Archive-663/olympusPENF/ASSETS/PHOTO/samplePOS_PENF (1).jpg

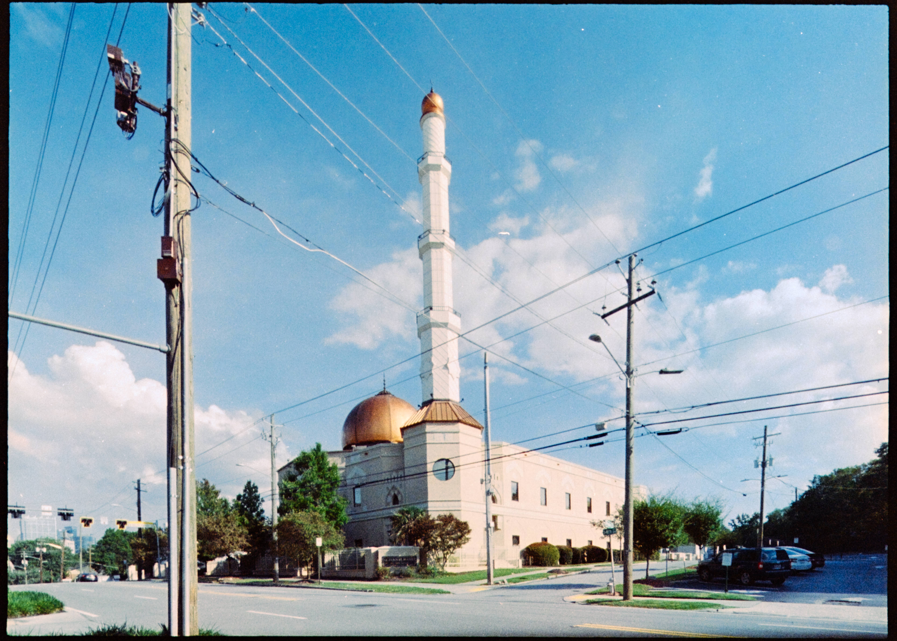
ASSETS/PHOTO/samplePOS_PENF (1).jpg
