Archive-663/olympusPENF/ASSETS/PHOTO/samplePOS_PENF (2).jpg

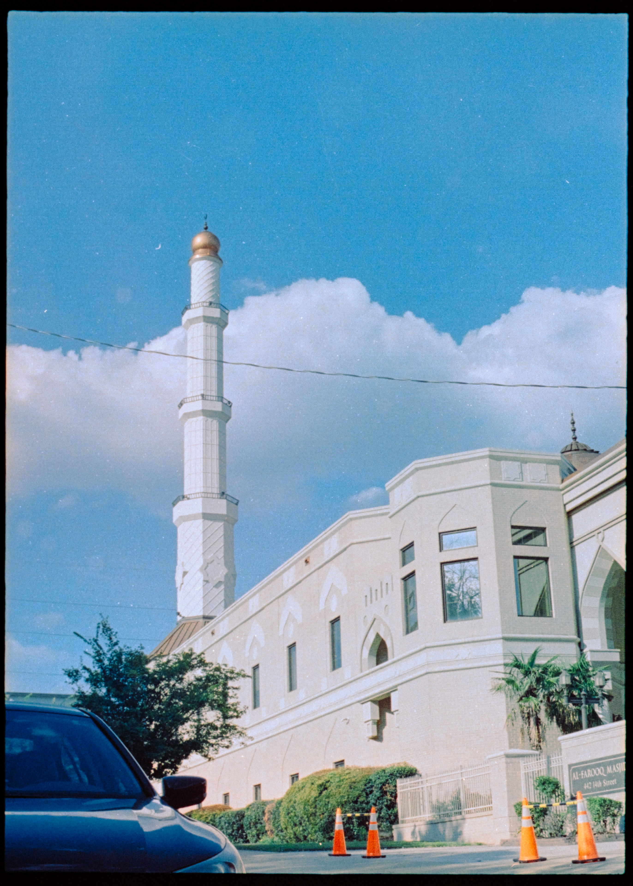
ASSETS/PHOTO/samplePOS_PENF (2).jpg
