Archive-663/olympusPENF/ASSETS/PHOTO/samplePOS_PENF (3).jpg

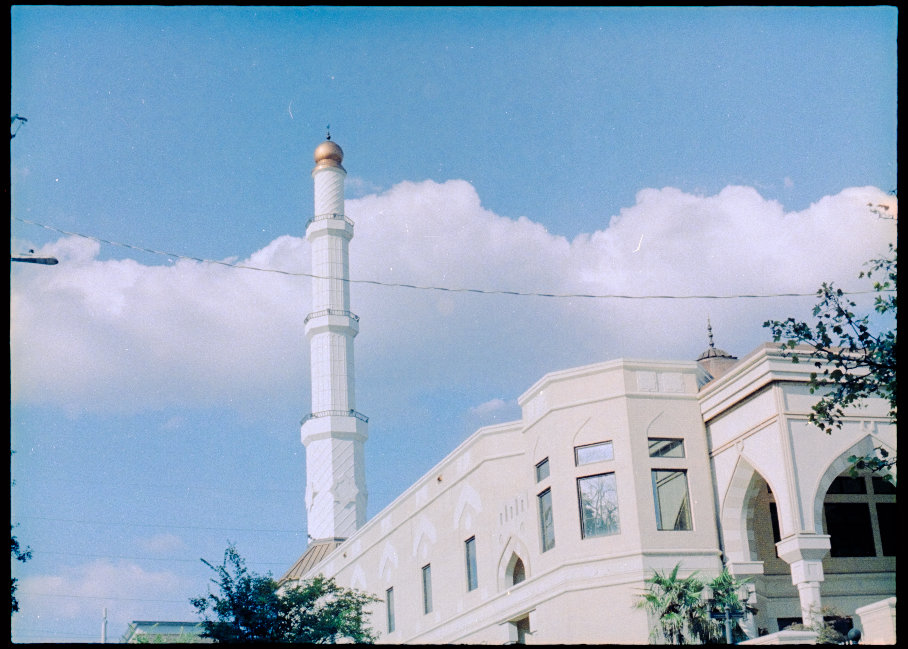
ASSETS/PHOTO/samplePOS_PENF (3).jpg
