Archive-663/olympusPENF/ASSETS/PHOTO/samplePOS_PENF (5).jpg

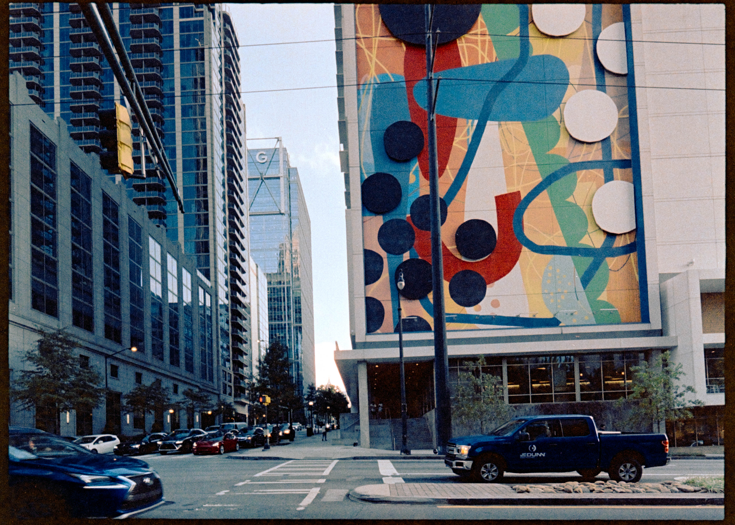
ASSETS/PHOTO/samplePOS_PENF (5).jpg
