Archive-663/olympusPENF/ASSETS/PHOTO/samplePOS_PENF (6).jpg

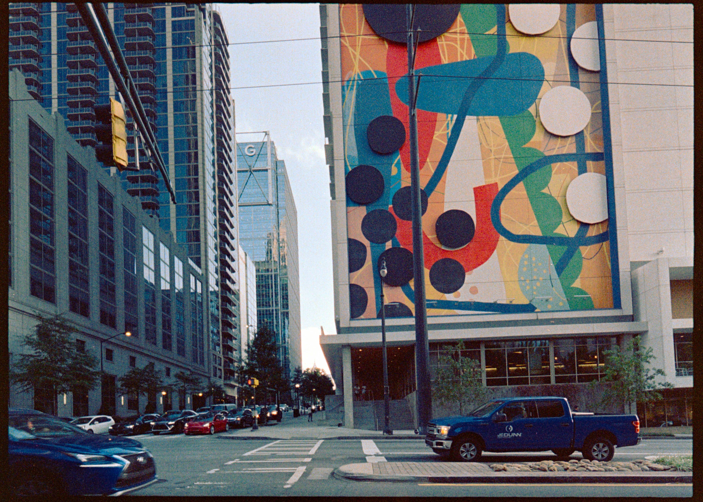
ASSETS/PHOTO/samplePOS_PENF (6).jpg
