Archive-663/olympusPENF/ASSETS/PHOTO/samplePOS_PENF (7).jpg

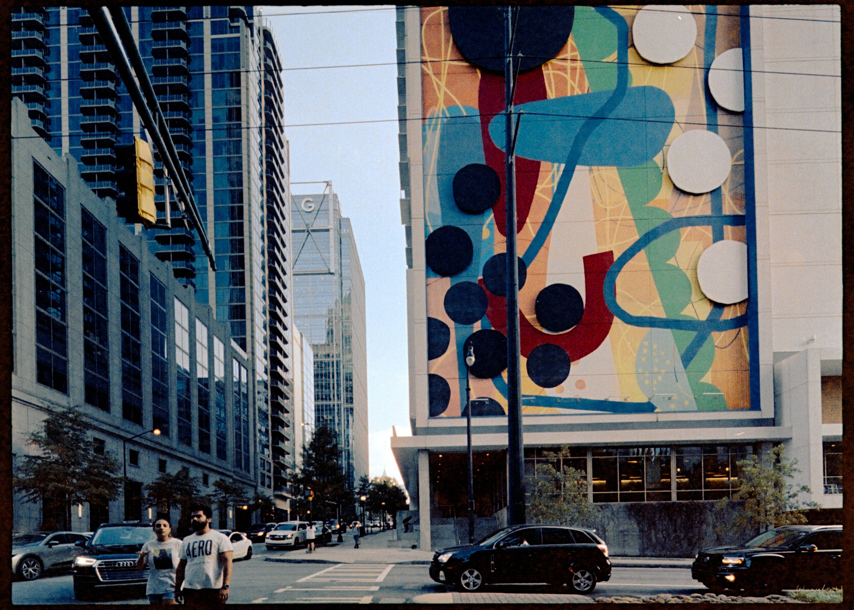
ASSETS/PHOTO/samplePOS_PENF (7).jpg
