Archive-663/olympusPENF/ASSETS/PHOTO/samplePOS_PENF (8).jpg

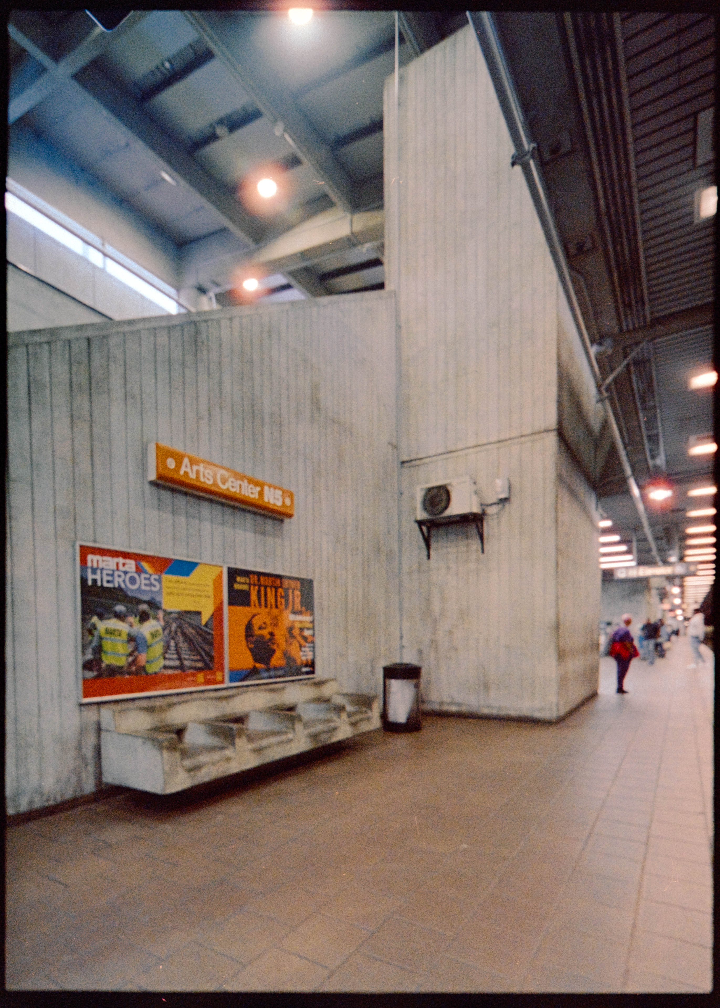
ASSETS/PHOTO/samplePOS_PENF (8).jpg
