Archive-663/olympusPENF/ASSETS/PHOTO/samplePOS_PENF (9).jpg

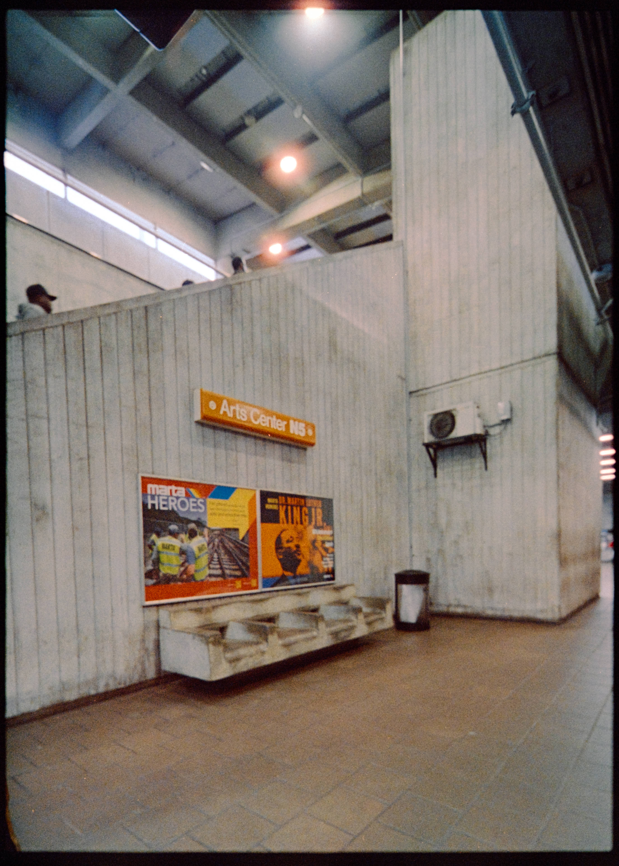
ASSETS/PHOTO/samplePOS_PENF (9).jpg
