Archive-663/olympusPENF/ASSETS/PHOTO/samplePOS_PENF (10).jpg

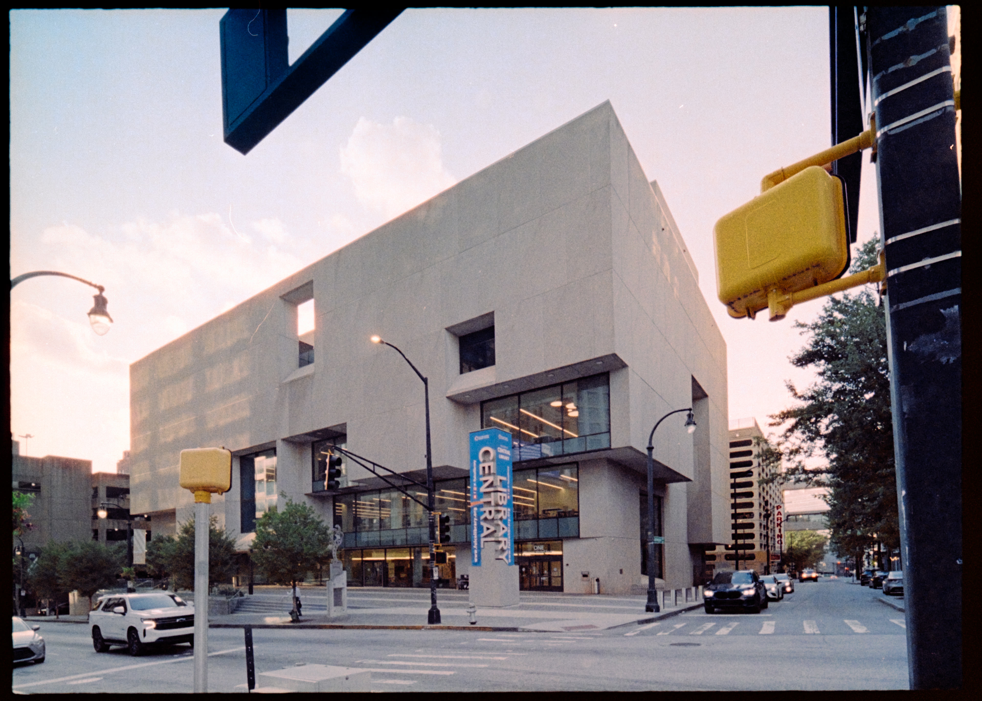
ASSETS/PHOTO/samplePOS_PENF (10).jpg
