Archive-663/olympusPENF/ASSETS/PHOTO/samplePOS_PENF (12).jpg

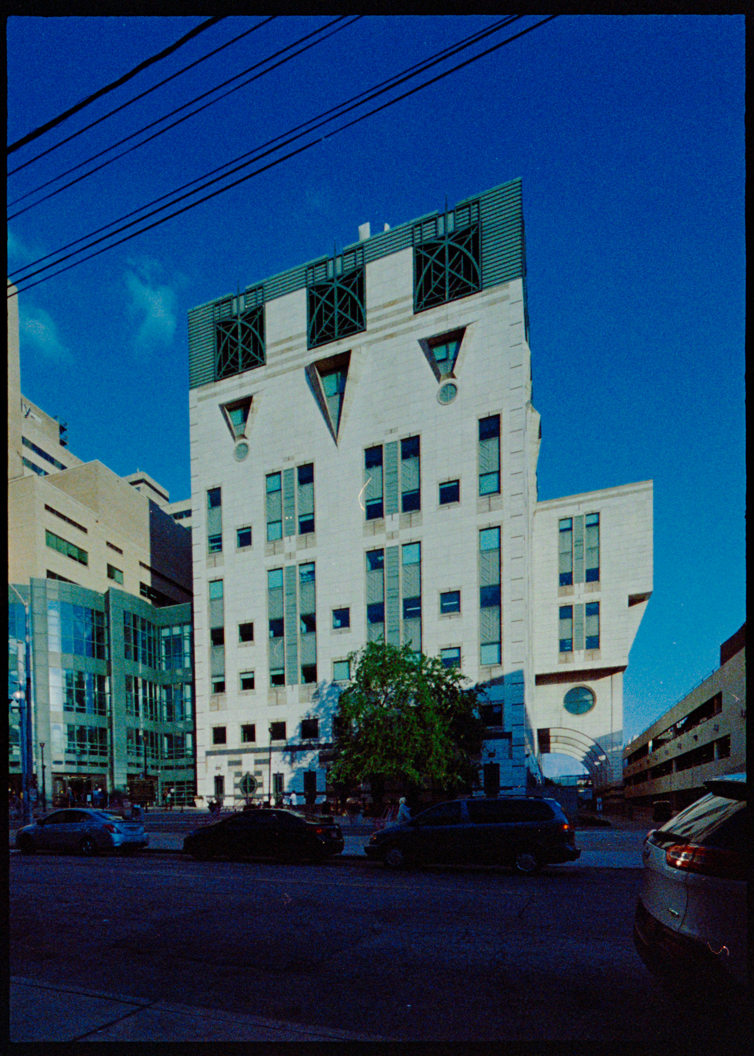
ASSETS/PHOTO/samplePOS_PENF (12).jpg
