Archive-663/olympusPENF/ASSETS/PHOTO/samplePOS_PENF (13).jpg

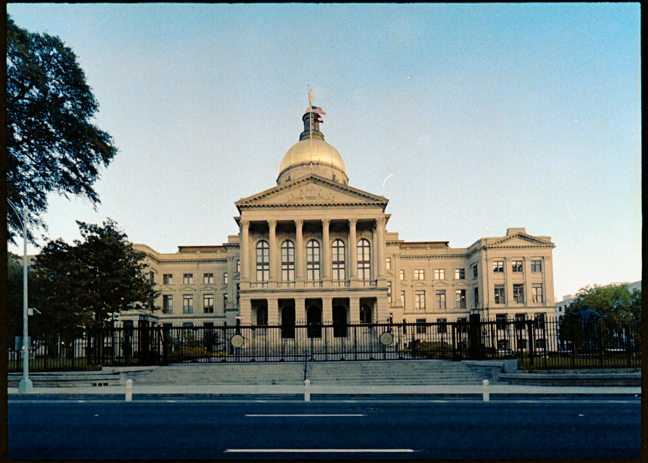
ASSETS/PHOTO/samplePOS_PENF (13).jpg
