Archive-663/olympusPENF/ASSETS/PHOTO/samplePOS_PENF (15).jpg

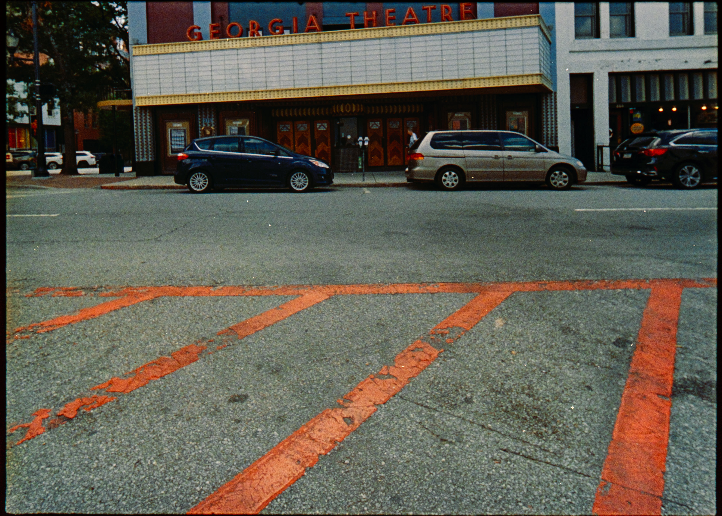
ASSETS/PHOTO/samplePOS_PENF (15).jpg
