Archive-663/olympusPENF/ASSETS/PHOTO/samplePOS_PENF (16).jpg

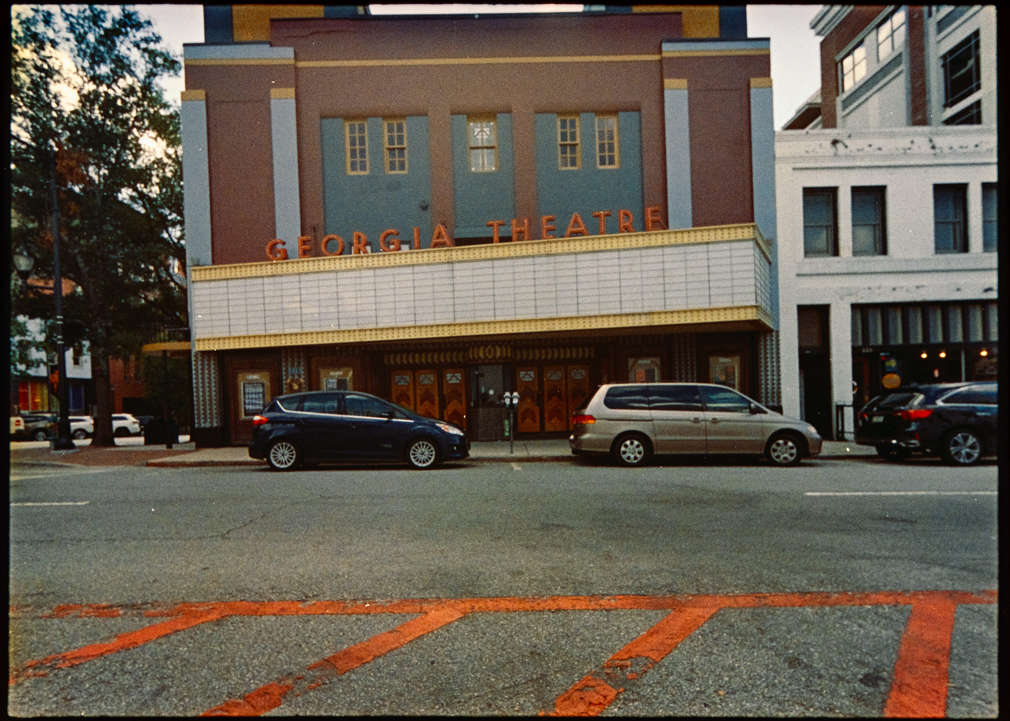
ASSETS/PHOTO/samplePOS_PENF (16).jpg
