Archive-663/olympusPENF/ASSETS/PHOTO/samplePOS_PENF (17).jpg

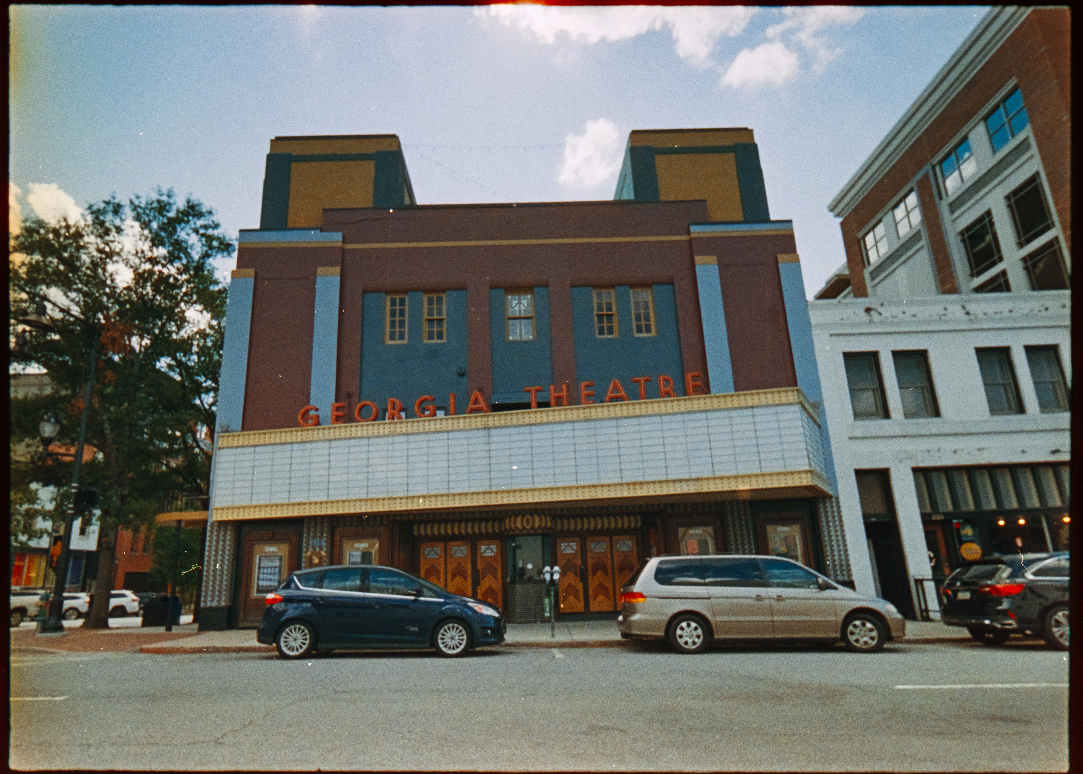
ASSETS/PHOTO/samplePOS_PENF (17).jpg
