Archive-663/olympusPENF/ASSETS/PHOTO/samplePOS_PENF (18).jpg

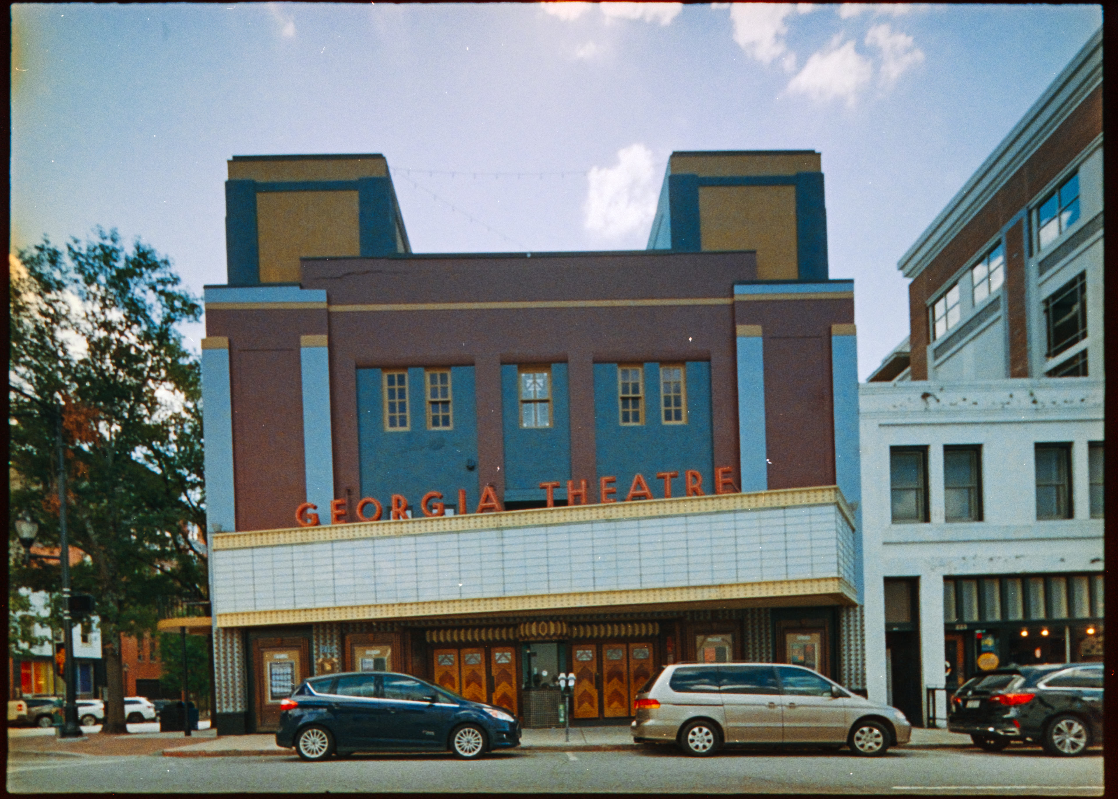
ASSETS/PHOTO/samplePOS_PENF (18).jpg
