Archive-663/olympusPENF/ASSETS/PHOTO/samplePOS_PENF (19).jpg

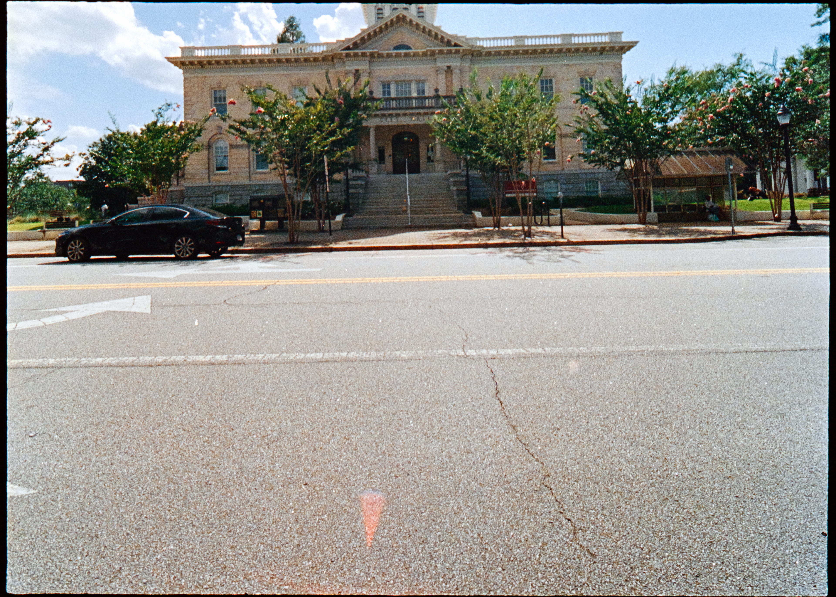
ASSETS/PHOTO/samplePOS_PENF (19).jpg
