Archive-663/olympusPENF/ASSETS/PHOTO/samplePOS_PENF (20).jpg

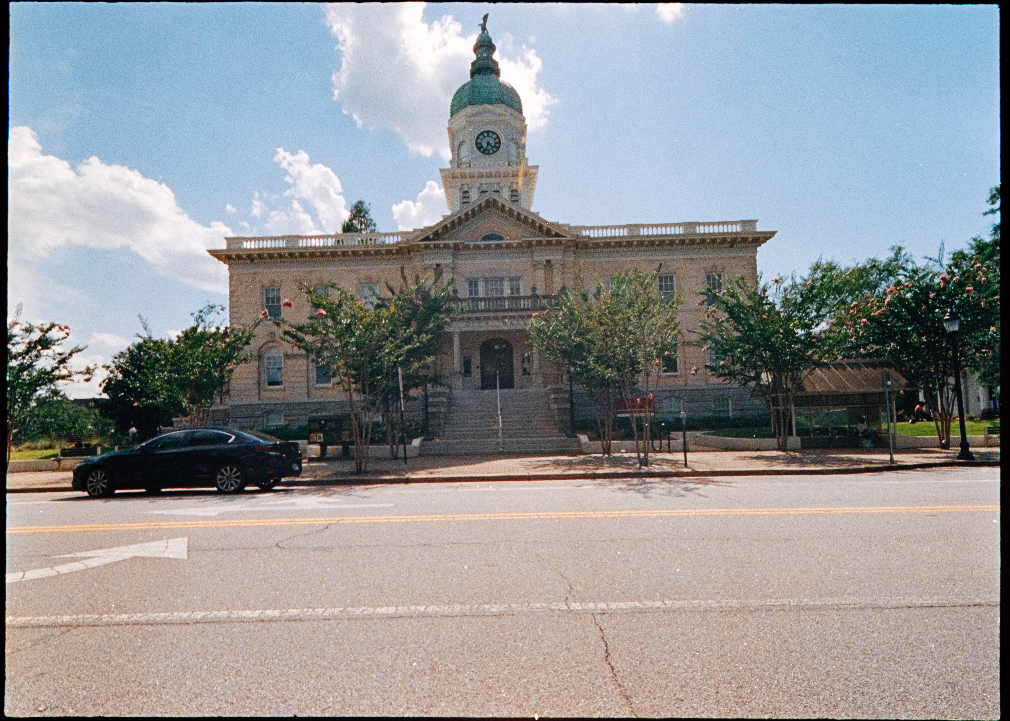
ASSETS/PHOTO/samplePOS_PENF (20).jpg
