Archive-663/olympusPENF/ASSETS/PHOTO/samplePOS_PENF (21).jpg

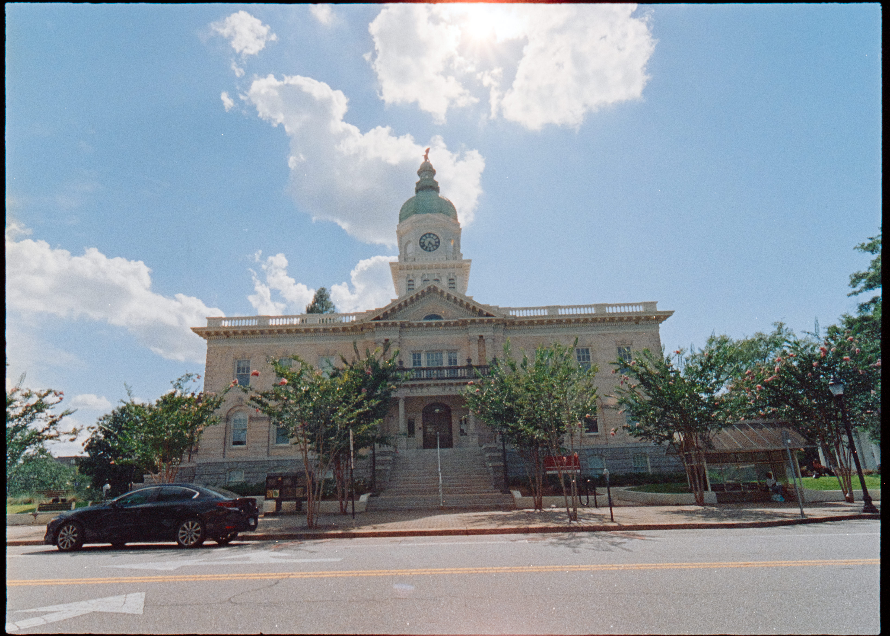
ASSETS/PHOTO/samplePOS_PENF (21).jpg
