Archive-663/olympusPENF/ASSETS/PHOTO/samplePOS_PENF (22).jpg

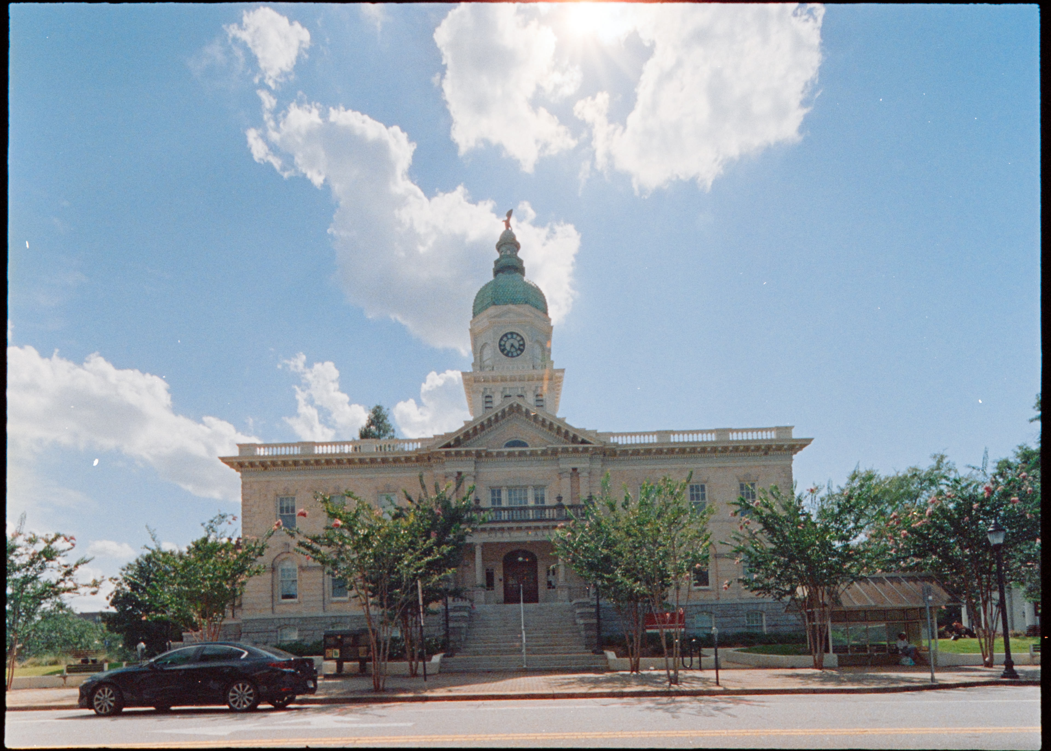
ASSETS/PHOTO/samplePOS_PENF (22).jpg
