Archive-663/olympusPENF/ASSETS/PHOTO/samplePOS_PENF (23).jpg

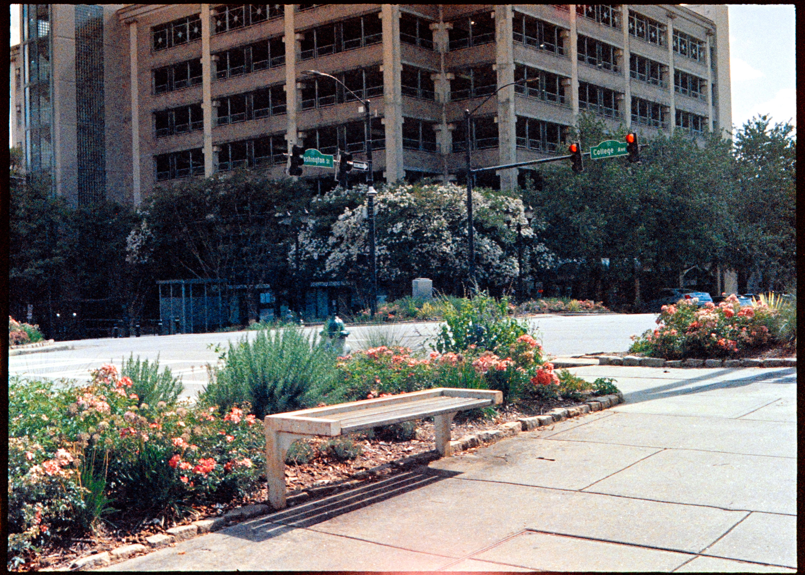
ASSETS/PHOTO/samplePOS_PENF (23).jpg
