Archive-663/olympusPENF/ASSETS/PHOTO/samplePOS_PENF (24).jpg

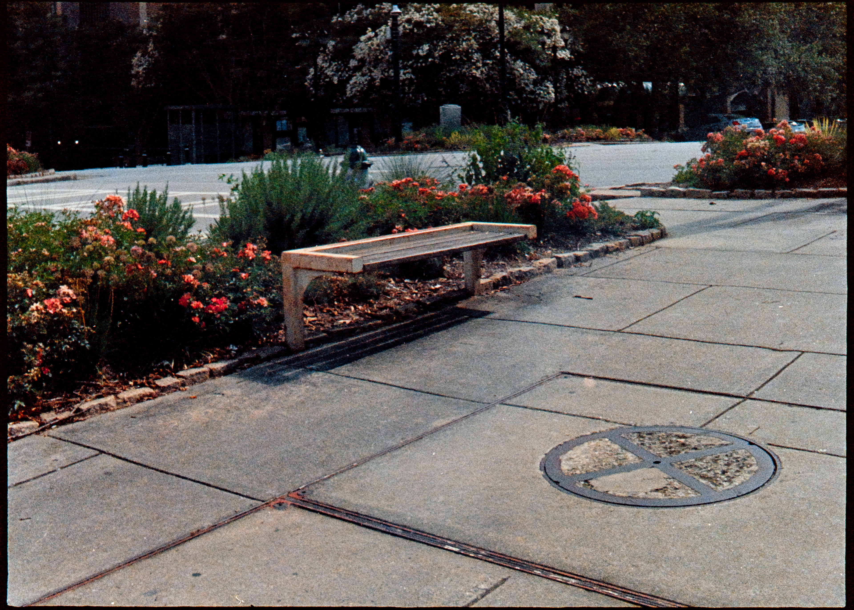
ASSETS/PHOTO/samplePOS_PENF (24).jpg
