Archive-663/olympusPENF/ASSETS/PHOTO/samplePOS_PENF (25).jpg

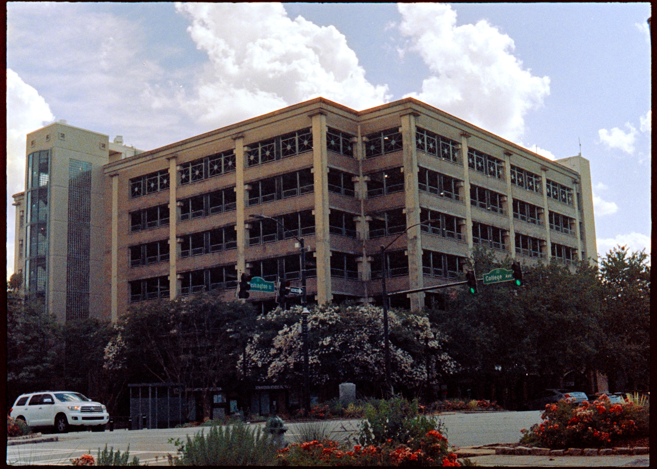
ASSETS/PHOTO/samplePOS_PENF (25).jpg
