Archive-663/olympusPENF/ASSETS/PHOTO/samplePOS_PENF (26).jpg

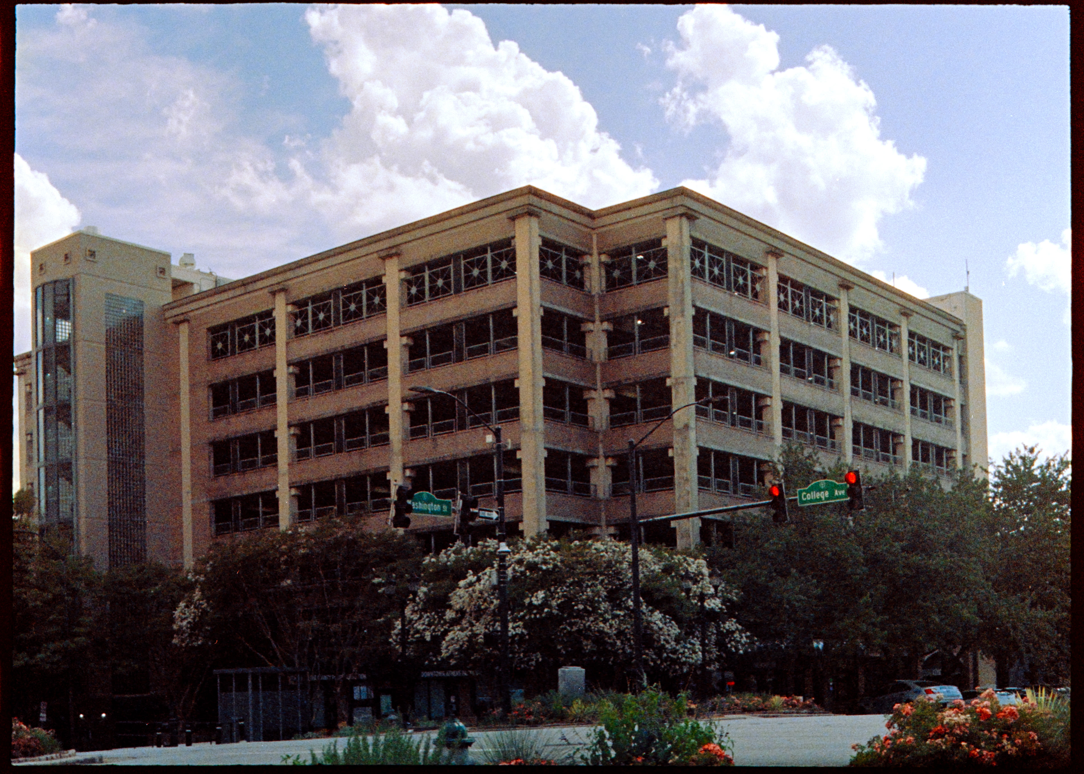
ASSETS/PHOTO/samplePOS_PENF (26).jpg
