Archive-663/olympusPENF/ASSETS/PHOTO/samplePOS_PENF (27).jpg

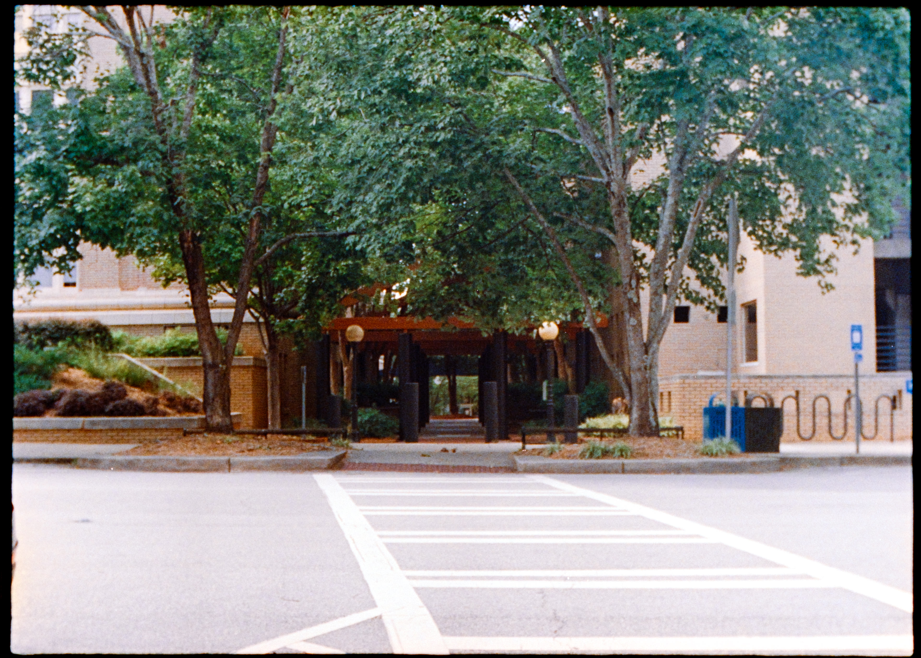
ASSETS/PHOTO/samplePOS_PENF (27).jpg
