Archive-663/olympusPENF/ASSETS/PHOTO/samplePOS_PENF (28).jpg

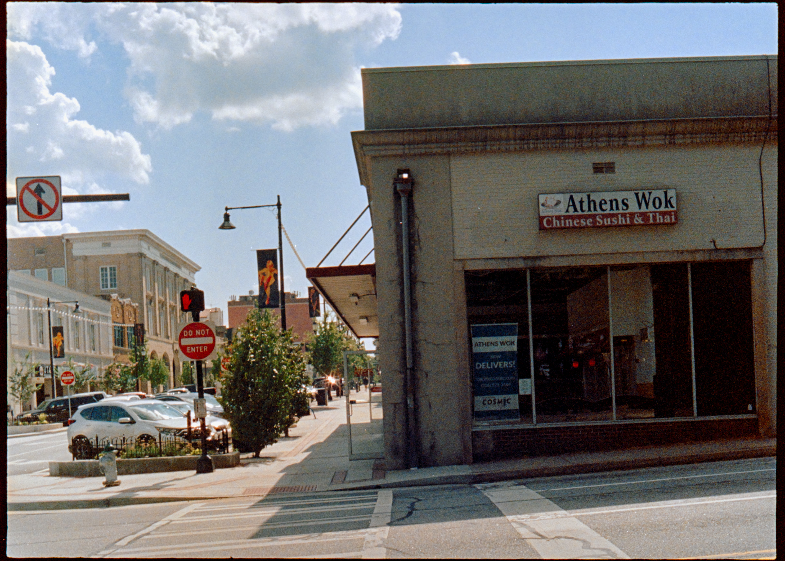
ASSETS/PHOTO/samplePOS_PENF (28).jpg
