Archive-663/olympusPENF/ASSETS/PHOTO/samplePOS_PENF (29).jpg

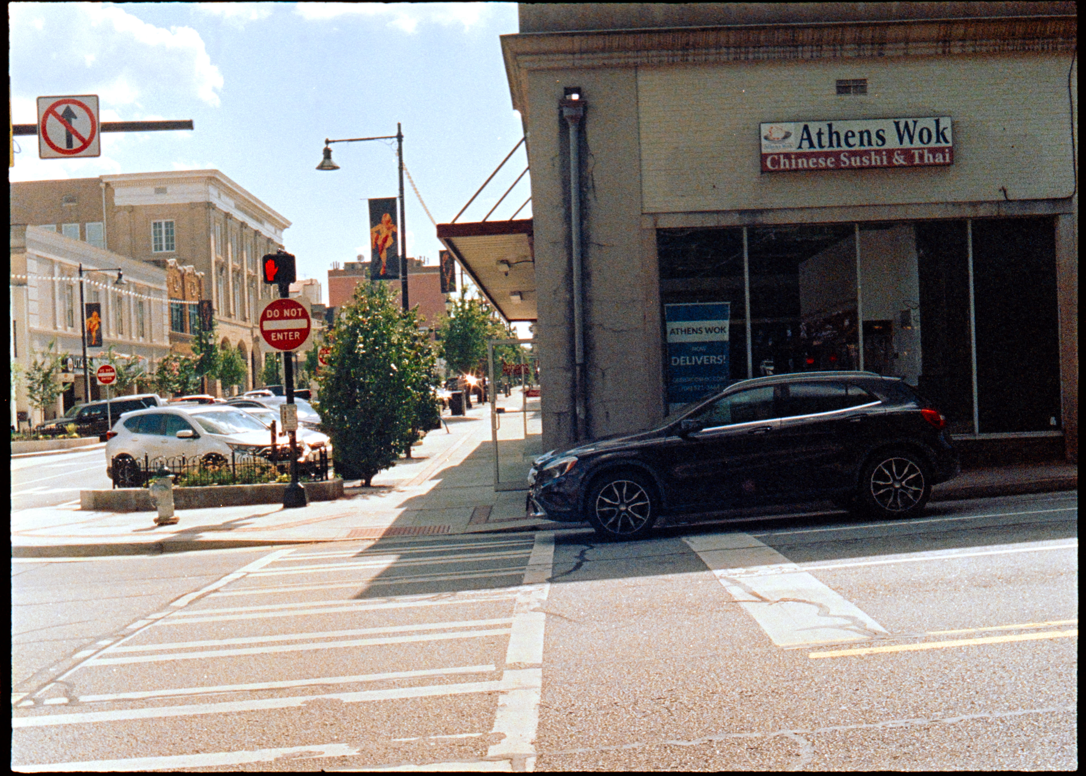
ASSETS/PHOTO/samplePOS_PENF (29).jpg
