Archive-663/olympusPENF/ASSETS/PHOTO/samplePOS_PENF (31).jpg

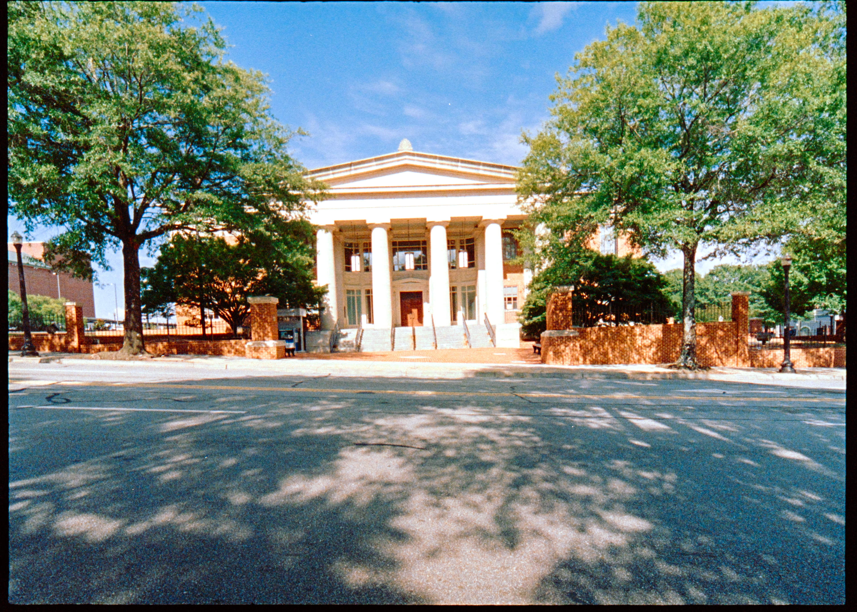
ASSETS/PHOTO/samplePOS_PENF (31).jpg
