Archive-663/olympusPENF/ASSETS/PHOTO/samplePOS_PENF (33).jpg

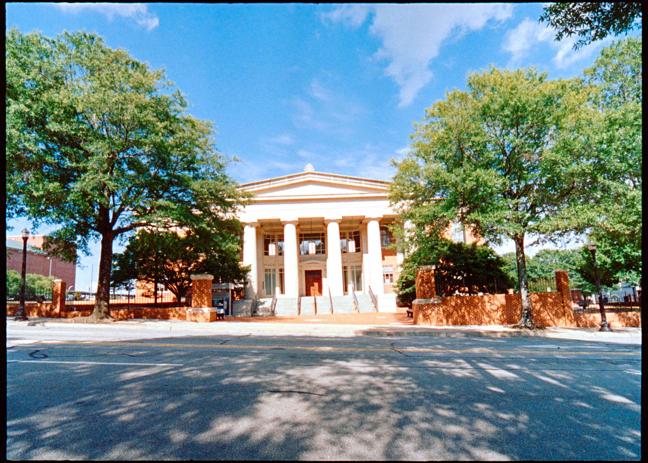
ASSETS/PHOTO/samplePOS_PENF (33).jpg
