Archive-663/olympusPENF/ASSETS/PHOTO/samplePOS_PENF (34).jpg

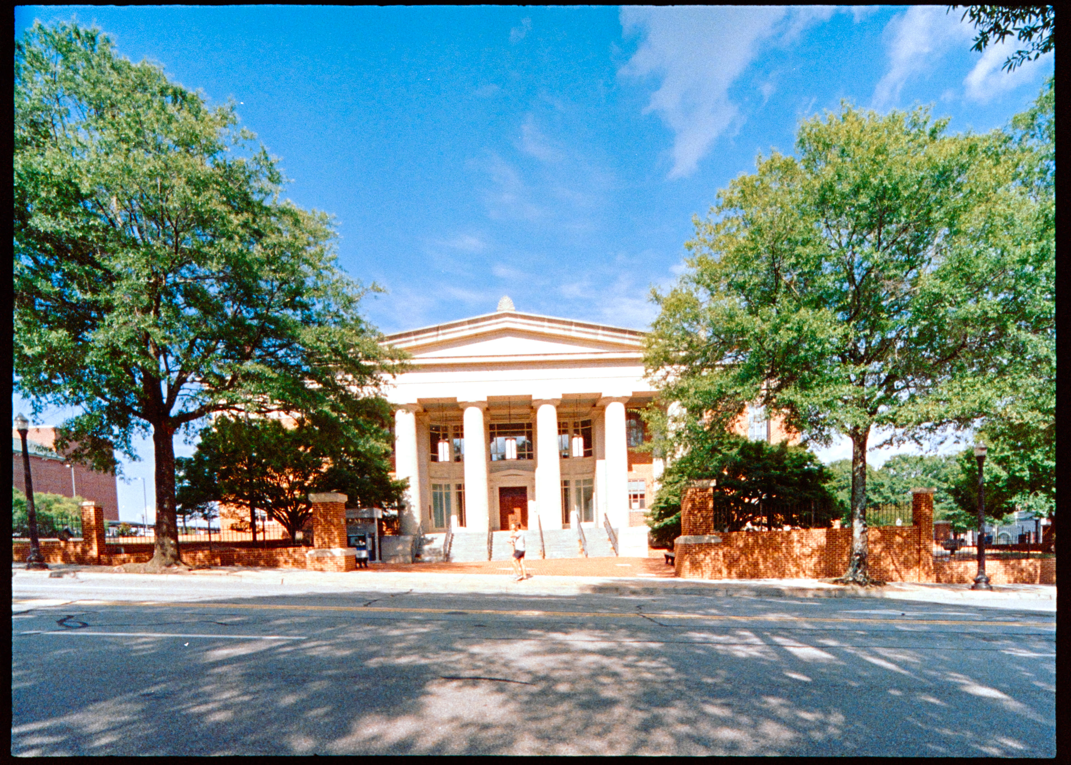
ASSETS/PHOTO/samplePOS_PENF (34).jpg
