Archive-663/olympusPENF/ASSETS/PHOTO/samplePOS_PENF (35).jpg

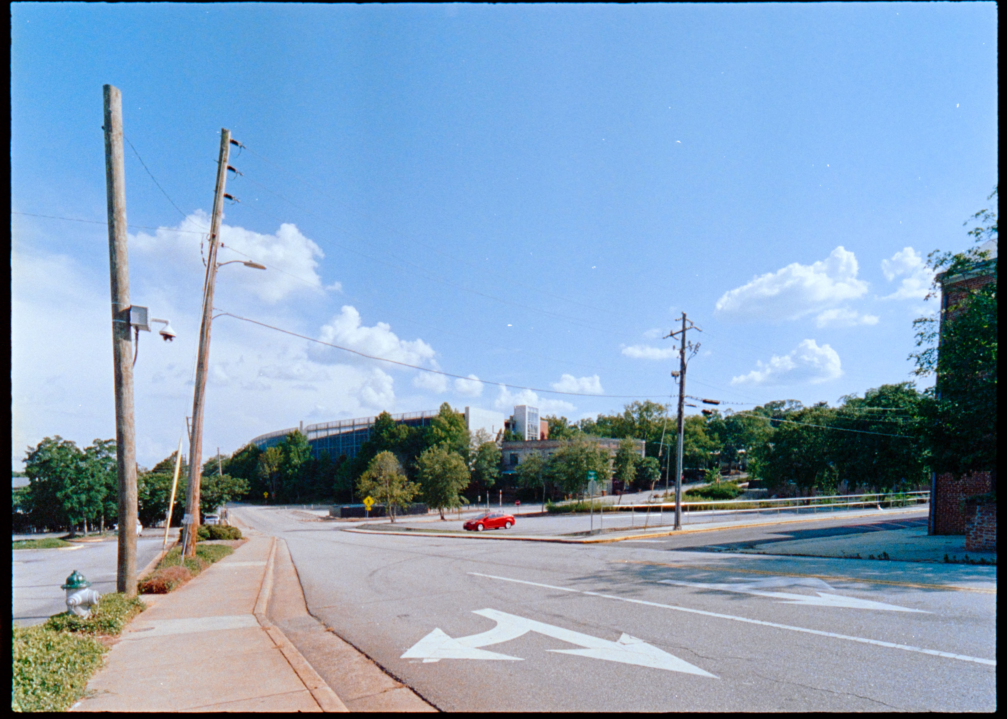
ASSETS/PHOTO/samplePOS_PENF (35).jpg
