Archive-663/olympusPENF/ASSETS/PHOTO/samplePOS_PENF (37).jpg

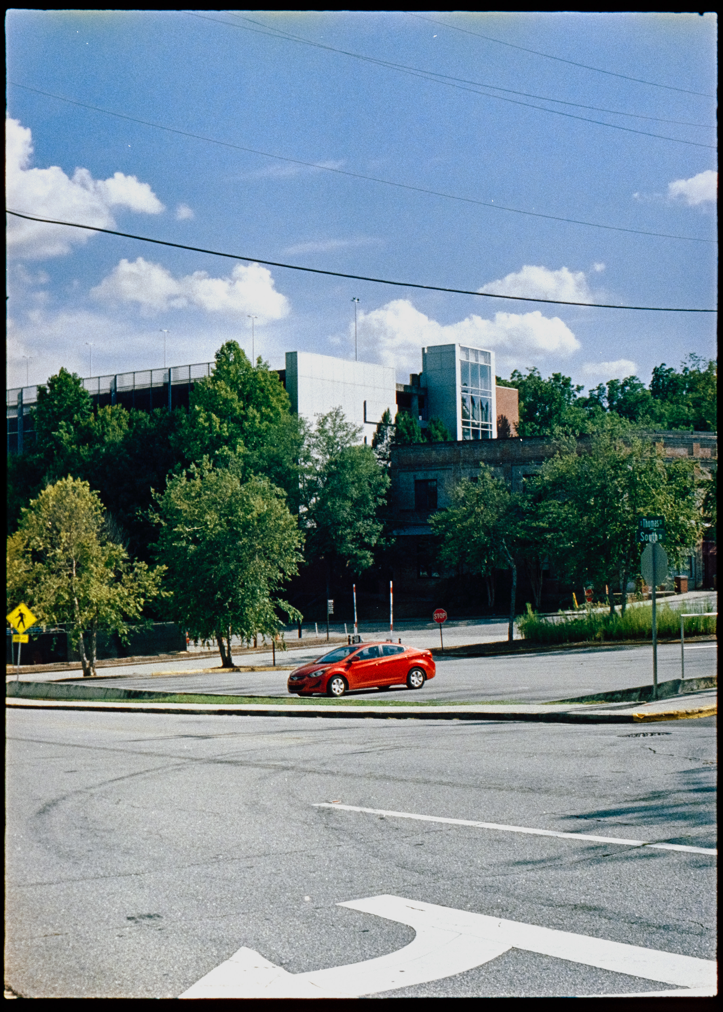
ASSETS/PHOTO/samplePOS_PENF (37).jpg
