Archive-663/olympusPENF/ASSETS/PHOTO/samplePOS_PENF (38).jpg

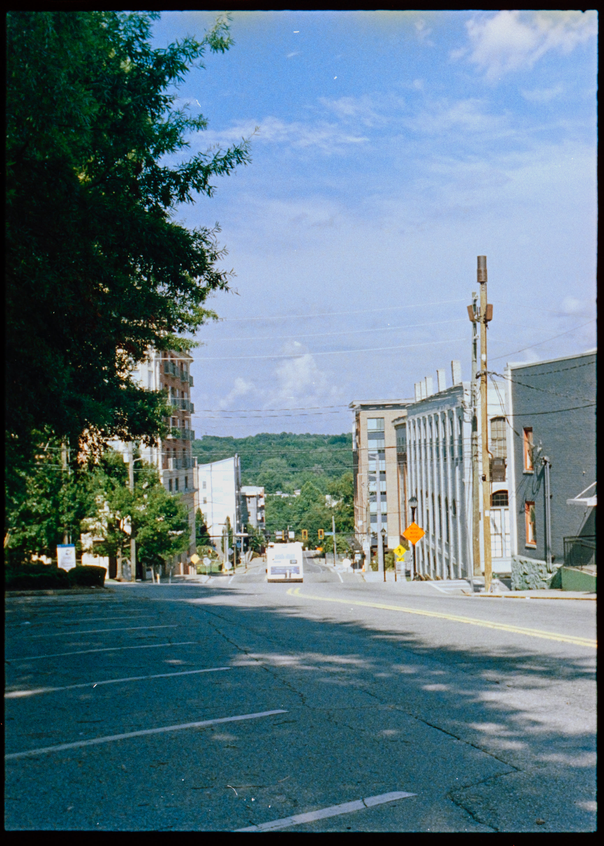
ASSETS/PHOTO/samplePOS_PENF (38).jpg
