Archive-663/olympusPENF/ASSETS/PHOTO/samplePOS_PENF (40).jpg

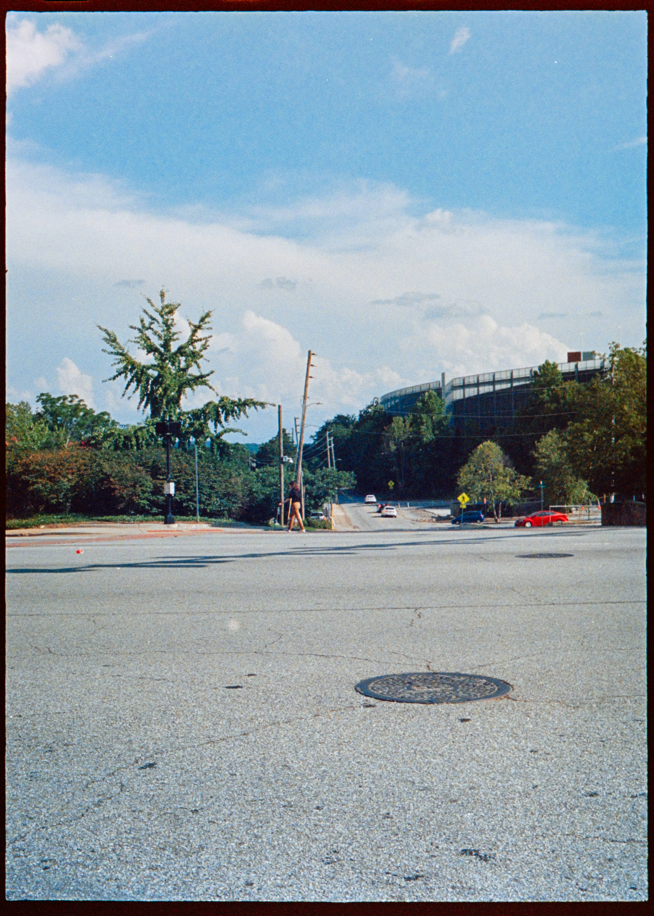
ASSETS/PHOTO/samplePOS_PENF (40).jpg
