Archive-663/olympusPENF/ASSETS/PHOTO/samplePOS_PENF (41).jpg

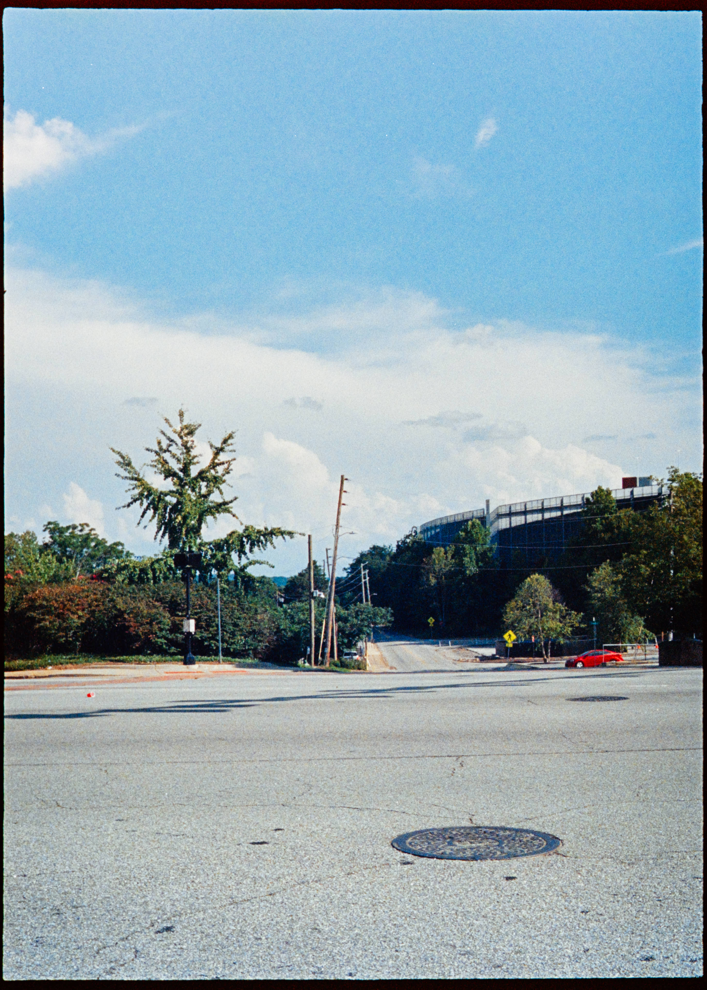
ASSETS/PHOTO/samplePOS_PENF (41).jpg
