Archive-663/olympusPENF/ASSETS/PHOTO/samplePOS_PENF (43).jpg

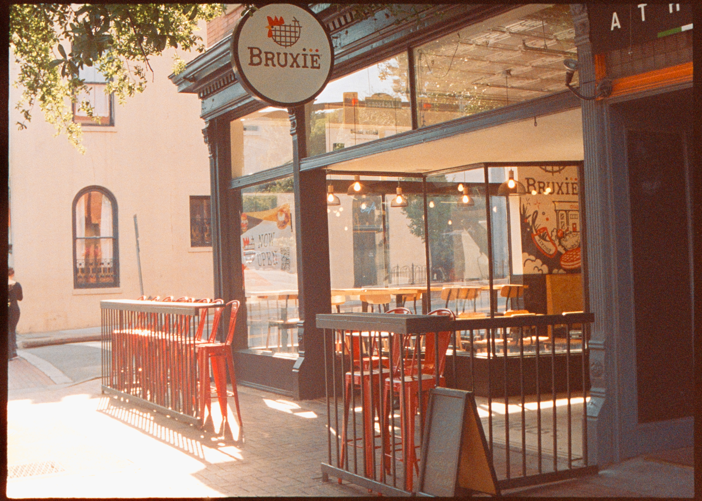
ASSETS/PHOTO/samplePOS_PENF (43).jpg
