Archive-663/olympusPENF/ASSETS/PHOTO/samplePOS_PENF (44).jpg

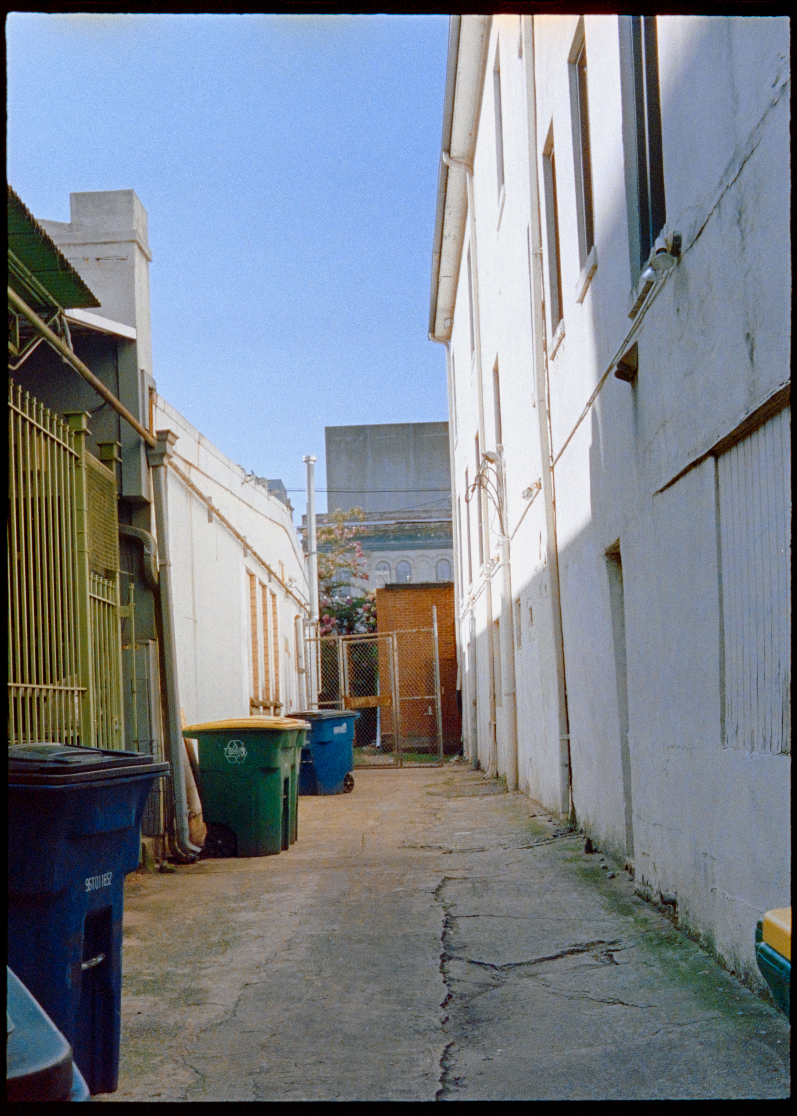
ASSETS/PHOTO/samplePOS_PENF (44).jpg
