Archive-663/olympusPENF/ASSETS/PRODUCT/product_PENF (5).jpg

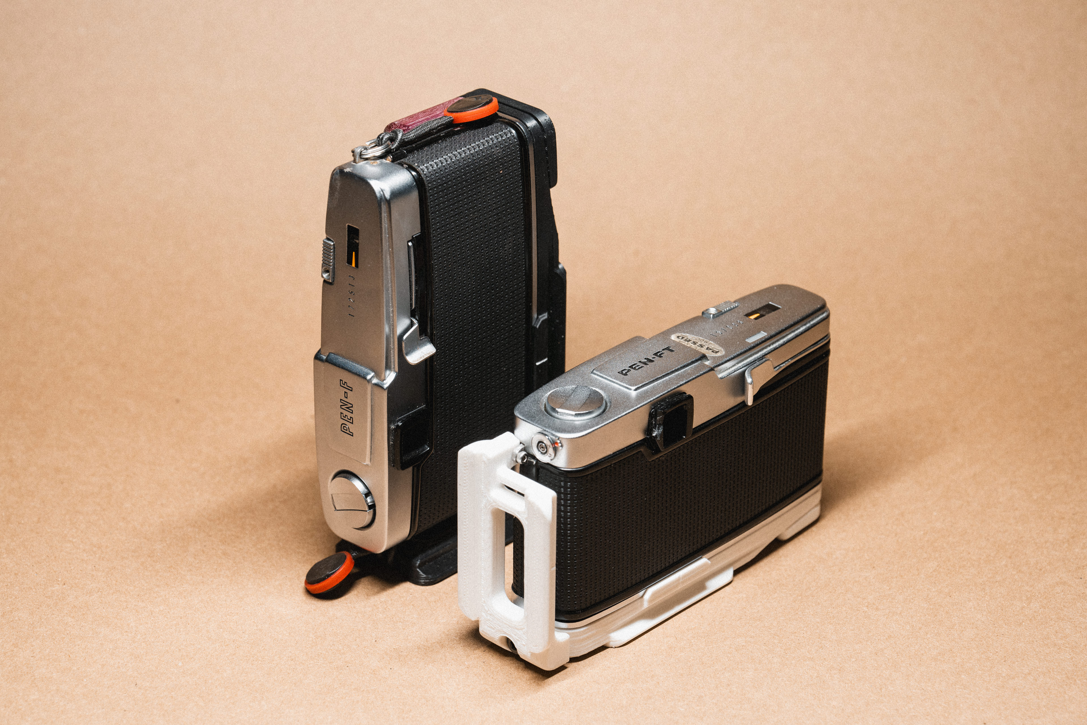
ASSETS/PRODUCT/product_PENF (5).jpg
