Archive-663/olympusPENF/ASSETS/PRODUCT/product_PENF (6).jpg

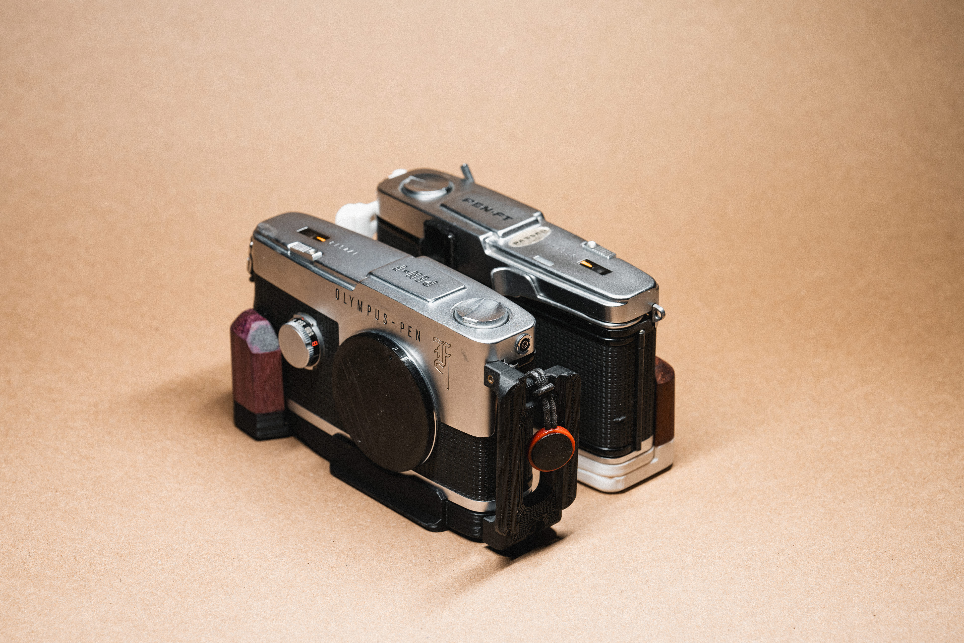
ASSETS/PRODUCT/product_PENF (6).jpg
